peng-zhihui/HelloWord-Keyboard/2.Firmware/HelloWord-Dynamic-fw/Core/Src/tim.c

/**
  ******************************************************************************
  * @file    tim.c
  * @brief   This file provides code for the configuration
  *          of the TIM instances.
  ******************************************************************************
  * @attention
  *
  * <h2><center>&copy; Copyright (c) 2022 STMicroelectronics.
  * All rights reserved.</center></h2>
  *
  * This software component is licensed by ST under Ultimate Liberty license
  * SLA0044, the "License"; You may not use this file except in compliance with
  * the License. You may obtain a copy of the License at:
  *                             www.st.com/SLA0044
  *
  ******************************************************************************
  */

/* Includes ------------------------------------------------------------------*/
#include "tim.h"

/* USER CODE BEGIN 0 */
volatile int64_t encCntLoop[2];

/* USER CODE END 0 */

TIM_HandleTypeDef htim1;
TIM_HandleTypeDef htim7;
TIM_HandleTypeDef htim9;
TIM_HandleTypeDef htim10;
TIM_HandleTypeDef htim11;
TIM_HandleTypeDef htim13;
TIM_HandleTypeDef htim14;

/* TIM1 init function */
void MX_TIM1_Init(void)
{

  TIM_MasterConfigTypeDef sMasterConfig = {0};
  TIM_OC_InitTypeDef sConfigOC = {0};
  TIM_BreakDeadTimeConfigTypeDef sBreakDeadTimeConfig = {0};

  htim1.Instance = TIM1;
  htim1.Init.Prescaler = 0;
  htim1.Init.CounterMode = TIM_COUNTERMODE_CENTERALIGNED1;
  htim1.Init.Period = 4199;
  htim1.Init.ClockDivision = TIM_CLOCKDIVISION_DIV1;
  htim1.Init.RepetitionCounter = 0;
  htim1.Init.AutoReloadPreload = TIM_AUTORELOAD_PRELOAD_DISABLE;
  if (HAL_TIM_PWM_Init(&htim1) != HAL_OK)
  {
    Error_Handler();
  }
  sMasterConfig.MasterOutputTrigger = TIM_TRGO_OC4REF;
  sMasterConfig.MasterSlaveMode = TIM_MASTERSLAVEMODE_DISABLE;
  if (HAL_TIMEx_MasterConfigSynchronization(&htim1, &sMasterConfig) != HAL_OK)
  {
    Error_Handler();
  }
  sConfigOC.OCMode = TIM_OCMODE_PWM1;
  sConfigOC.Pulse = 0;
  sConfigOC.OCPolarity = TIM_OCPOLARITY_HIGH;
  sConfigOC.OCNPolarity = TIM_OCNPOLARITY_HIGH;
  sConfigOC.OCFastMode = TIM_OCFAST_DISABLE;
  sConfigOC.OCIdleState = TIM_OCIDLESTATE_RESET;
  sConfigOC.OCNIdleState = TIM_OCNIDLESTATE_RESET;
  if (HAL_TIM_PWM_ConfigChannel(&htim1, &sConfigOC, TIM_CHANNEL_1) != HAL_OK)
  {
    Error_Handler();
  }
  if (HAL_TIM_PWM_ConfigChannel(&htim1, &sConfigOC, TIM_CHANNEL_2) != HAL_OK)
  {
    Error_Handler();
  }
  if (HAL_TIM_PWM_ConfigChannel(&htim1, &sConfigOC, TIM_CHANNEL_3) != HAL_OK)
  {
    Error_Handler();
  }
  sBreakDeadTimeConfig.OffStateRunMode = TIM_OSSR_DISABLE;
  sBreakDeadTimeConfig.OffStateIDLEMode = TIM_OSSI_DISABLE;
  sBreakDeadTimeConfig.LockLevel = TIM_LOCKLEVEL_OFF;
  sBreakDeadTimeConfig.DeadTime = 0;
  sBreakDeadTimeConfig.BreakState = TIM_BREAK_DISABLE;
  sBreakDeadTimeConfig.BreakPolarity = TIM_BREAKPOLARITY_HIGH;
  sBreakDeadTimeConfig.AutomaticOutput = TIM_AUTOMATICOUTPUT_DISABLE;
  if (HAL_TIMEx_ConfigBreakDeadTime(&htim1, &sBreakDeadTimeConfig) != HAL_OK)
  {
    Error_Handler();
  }
  HAL_TIM_MspPostInit(&htim1);

}
/* TIM7 init function */
void MX_TIM7_Init(void)
{

  TIM_MasterConfigTypeDef sMasterConfig = {0};

  htim7.Instance = TIM7;
  htim7.Init.Prescaler = 83;
  htim7.Init.CounterMode = TIM_COUNTERMODE_UP;
  htim7.Init.Period = 9999;
  htim7.Init.AutoReloadPreload = TIM_AUTORELOAD_PRELOAD_ENABLE;
  if (HAL_TIM_Base_Init(&htim7) != HAL_OK)
  {
    Error_Handler();
  }
  sMasterConfig.MasterOutputTrigger = TIM_TRGO_RESET;
  sMasterConfig.MasterSlaveMode = TIM_MASTERSLAVEMODE_DISABLE;
  if (HAL_TIMEx_MasterConfigSynchronization(&htim7, &sMasterConfig) != HAL_OK)
  {
    Error_Handler();
  }
}
/* TIM9 init function */
void MX_TIM9_Init(void)
{

  TIM_ClockConfigTypeDef sClockSourceConfig = {0};

  htim9.Instance = TIM9;
  htim9.Init.Prescaler = 0;
  htim9.Init.CounterMode = TIM_COUNTERMODE_UP;
  htim9.Init.Period = 65535;
  htim9.Init.ClockDivision = TIM_CLOCKDIVISION_DIV1;
  htim9.Init.AutoReloadPreload = TIM_AUTORELOAD_PRELOAD_DISABLE;
  if (HAL_TIM_Base_Init(&htim9) != HAL_OK)
  {
    Error_Handler();
  }
  sClockSourceConfig.ClockSource = TIM_CLOCKSOURCE_INTERNAL;
  if (HAL_TIM_ConfigClockSource(&htim9, &sClockSourceConfig) != HAL_OK)
  {
    Error_Handler();
  }
}
/* TIM10 init function */
void MX_TIM10_Init(void)
{

  htim10.Instance = TIM10;
  htim10.Init.Prescaler = 167;
  htim10.Init.CounterMode = TIM_COUNTERMODE_UP;
  htim10.Init.Period = 9999;
  htim10.Init.ClockDivision = TIM_CLOCKDIVISION_DIV1;
  htim10.Init.AutoReloadPreload = TIM_AUTORELOAD_PRELOAD_ENABLE;
  if (HAL_TIM_Base_Init(&htim10) != HAL_OK)
  {
    Error_Handler();
  }
}
/* TIM11 init function */
void MX_TIM11_Init(void)
{

  htim11.Instance = TIM11;
  htim11.Init.Prescaler = 167;
  htim11.Init.CounterMode = TIM_COUNTERMODE_UP;
  htim11.Init.Period = 9999;
  htim11.Init.ClockDivision = TIM_CLOCKDIVISION_DIV1;
  htim11.Init.AutoReloadPreload = TIM_AUTORELOAD_PRELOAD_DISABLE;
  if (HAL_TIM_Base_Init(&htim11) != HAL_OK)
  {
    Error_Handler();
  }
}
/* TIM13 init function */
void MX_TIM13_Init(void)
{

  htim13.Instance = TIM13;
  htim13.Init.Prescaler = 83;
  htim13.Init.CounterMode = TIM_COUNTERMODE_UP;
  htim13.Init.Period = 9999;
  htim13.Init.ClockDivision = TIM_CLOCKDIVISION_DIV1;
  htim13.Init.AutoReloadPreload = TIM_AUTORELOAD_PRELOAD_DISABLE;
  if (HAL_TIM_Base_Init(&htim13) != HAL_OK)
  {
    Error_Handler();
  }
}
/* TIM14 init function */
void MX_TIM14_Init(void)
{

  htim14.Instance = TIM14;
  htim14.Init.Prescaler = 83;
  htim14.Init.CounterMode = TIM_COUNTERMODE_UP;
  htim14.Init.Period = 9999;
  htim14.Init.ClockDivision = TIM_CLOCKDIVISION_DIV1;
  htim14.Init.AutoReloadPreload = TIM_AUTORELOAD_PRELOAD_DISABLE;
  if (HAL_TIM_Base_Init(&htim14) != HAL_OK)
  {
    Error_Handler();
  }
}

void HAL_TIM_PWM_MspInit(TIM_HandleTypeDef* tim_pwmHandle)
{

  if(tim_pwmHandle->Instance==TIM1)
  {
    /* TIM1 clock enable */
    __HAL_RCC_TIM1_CLK_ENABLE();

    /* TIM1 interrupt Init */
    HAL_NVIC_SetPriority(TIM1_UP_TIM10_IRQn, 5, 0);
    HAL_NVIC_EnableIRQ(TIM1_UP_TIM10_IRQn);
    HAL_NVIC_SetPriority(TIM1_TRG_COM_TIM11_IRQn, 5, 0);
    HAL_NVIC_EnableIRQ(TIM1_TRG_COM_TIM11_IRQn);
  }
}

void HAL_TIM_Base_MspInit(TIM_HandleTypeDef* tim_baseHandle)
{

  if(tim_baseHandle->Instance==TIM7)
  {
    /* TIM7 clock enable */
    __HAL_RCC_TIM7_CLK_ENABLE();

    /* TIM7 interrupt Init */
    HAL_NVIC_SetPriority(TIM7_IRQn, 5, 0);
    HAL_NVIC_EnableIRQ(TIM7_IRQn);
  }
  else if(tim_baseHandle->Instance==TIM9)
  {
    /* TIM9 clock enable */
    __HAL_RCC_TIM9_CLK_ENABLE();
  }
  else if(tim_baseHandle->Instance==TIM10)
  {
    /* TIM10 clock enable */
    __HAL_RCC_TIM10_CLK_ENABLE();

    /* TIM10 interrupt Init */
    HAL_NVIC_SetPriority(TIM1_UP_TIM10_IRQn, 5, 0);
    HAL_NVIC_EnableIRQ(TIM1_UP_TIM10_IRQn);
  }
  else if(tim_baseHandle->Instance==TIM11)
  {
    /* TIM11 clock enable */
    __HAL_RCC_TIM11_CLK_ENABLE();

    /* TIM11 interrupt Init */
    HAL_NVIC_SetPriority(TIM1_TRG_COM_TIM11_IRQn, 5, 0);
    HAL_NVIC_EnableIRQ(TIM1_TRG_COM_TIM11_IRQn);
  }
  else if(tim_baseHandle->Instance==TIM13)
  {
    /* TIM13 clock enable */
    __HAL_RCC_TIM13_CLK_ENABLE();

    /* TIM13 interrupt Init */
    HAL_NVIC_SetPriority(TIM8_UP_TIM13_IRQn, 5, 0);
    HAL_NVIC_EnableIRQ(TIM8_UP_TIM13_IRQn);
  }
  else if(tim_baseHandle->Instance==TIM14)
  {
    /* TIM14 clock enable */
    __HAL_RCC_TIM14_CLK_ENABLE();

    /* TIM14 interrupt Init */
    HAL_NVIC_SetPriority(TIM8_TRG_COM_TIM14_IRQn, 5, 0);
    HAL_NVIC_EnableIRQ(TIM8_TRG_COM_TIM14_IRQn);
  }
}
void HAL_TIM_MspPostInit(TIM_HandleTypeDef* timHandle)
{

  GPIO_InitTypeDef GPIO_InitStruct = {0};
  if(timHandle->Instance==TIM1)
  {
    __HAL_RCC_GPIOB_CLK_ENABLE();
    __HAL_RCC_GPIOA_CLK_ENABLE();
    /**TIM1 GPIO Configuration
    PB0     ------> TIM1_CH2N
    PB1     ------> TIM1_CH3N
    PB13     ------> TIM1_CH1N
    PA8     ------> TIM1_CH1
    PA9     ------> TIM1_CH2
    PA10     ------> TIM1_CH3
    */
    GPIO_InitStruct.Pin = M0_PWM_BL_Pin|M0_PWM_CL_Pin|M0_PWM_AL_Pin;
    GPIO_InitStruct.Mode = GPIO_MODE_AF_PP;
    GPIO_InitStruct.Pull = GPIO_NOPULL;
    GPIO_InitStruct.Speed = GPIO_SPEED_FREQ_VERY_HIGH;
    GPIO_InitStruct.Alternate = GPIO_AF1_TIM1;
    HAL_GPIO_Init(GPIOB, &GPIO_InitStruct);

    GPIO_InitStruct.Pin = M0_PWM_AH_Pin|M0_PWM_BH_Pin|M0_PWM_CH_Pin;
    GPIO_InitStruct.Mode = GPIO_MODE_AF_PP;
    GPIO_InitStruct.Pull = GPIO_NOPULL;
    GPIO_InitStruct.Speed = GPIO_SPEED_FREQ_VERY_HIGH;
    GPIO_InitStruct.Alternate = GPIO_AF1_TIM1;
    HAL_GPIO_Init(GPIOA, &GPIO_InitStruct);

  }

}

void HAL_TIM_PWM_MspDeInit(TIM_HandleTypeDef* tim_pwmHandle)
{

  if(tim_pwmHandle->Instance==TIM1)
  {
    /* Peripheral clock disable */
    __HAL_RCC_TIM1_CLK_DISABLE();

    /* TIM1 interrupt Deinit */
  /* USER CODE BEGIN TIM1:TIM1_UP_TIM10_IRQn disable */
    /**
    * Uncomment the line below to disable the "TIM1_UP_TIM10_IRQn" interrupt
    * Be aware, disabling shared interrupt may affect other IPs
    */
    /* HAL_NVIC_DisableIRQ(TIM1_UP_TIM10_IRQn); */
  /* USER CODE END TIM1:TIM1_UP_TIM10_IRQn disable */

  /* USER CODE BEGIN TIM1:TIM1_TRG_COM_TIM11_IRQn disable */
    /**
    * Uncomment the line below to disable the "TIM1_TRG_COM_TIM11_IRQn" interrupt
    * Be aware, disabling shared interrupt may affect other IPs
    */
    /* HAL_NVIC_DisableIRQ(TIM1_TRG_COM_TIM11_IRQn); */
  /* USER CODE END TIM1:TIM1_TRG_COM_TIM11_IRQn disable */

  }
}

void HAL_TIM_Base_MspDeInit(TIM_HandleTypeDef* tim_baseHandle)
{

  if(tim_baseHandle->Instance==TIM7)
  {
    /* Peripheral clock disable */
    __HAL_RCC_TIM7_CLK_DISABLE();

    /* TIM7 interrupt Deinit */
    HAL_NVIC_DisableIRQ(TIM7_IRQn);
  }
  else if(tim_baseHandle->Instance==TIM9)
  {
    /* Peripheral clock disable */
    __HAL_RCC_TIM9_CLK_DISABLE();
  }
  else if(tim_baseHandle->Instance==TIM10)
  {
    /* Peripheral clock disable */
    __HAL_RCC_TIM10_CLK_DISABLE();

    /* TIM10 interrupt Deinit */
  /* USER CODE BEGIN TIM10:TIM1_UP_TIM10_IRQn disable */
    /**
    * Uncomment the line below to disable the "TIM1_UP_TIM10_IRQn" interrupt
    * Be aware, disabling shared interrupt may affect other IPs
    */
    /* HAL_NVIC_DisableIRQ(TIM1_UP_TIM10_IRQn); */
  /* USER CODE END TIM10:TIM1_UP_TIM10_IRQn disable */

  }
  else if(tim_baseHandle->Instance==TIM11)
  {
    /* Peripheral clock disable */
    __HAL_RCC_TIM11_CLK_DISABLE();

    /* TIM11 interrupt Deinit */
  /* USER CODE BEGIN TIM11:TIM1_TRG_COM_TIM11_IRQn disable */
    /**
    * Uncomment the line below to disable the "TIM1_TRG_COM_TIM11_IRQn" interrupt
    * Be aware, disabling shared interrupt may affect other IPs
    */
    /* HAL_NVIC_DisableIRQ(TIM1_TRG_COM_TIM11_IRQn); */
  /* USER CODE END TIM11:TIM1_TRG_COM_TIM11_IRQn disable */

  }
  else if(tim_baseHandle->Instance==TIM13)
  {
    /* Peripheral clock disable */
    __HAL_RCC_TIM13_CLK_DISABLE();

    /* TIM13 interrupt Deinit */
    HAL_NVIC_DisableIRQ(TIM8_UP_TIM13_IRQn);
  }
  else if(tim_baseHandle->Instance==TIM14)
  {
    /* Peripheral clock disable */
    __HAL_RCC_TIM14_CLK_DISABLE();

    /* TIM14 interrupt Deinit */
    HAL_NVIC_DisableIRQ(TIM8_TRG_COM_TIM14_IRQn);
  }
}

/* USER CODE BEGIN 1 */
void HAL_TIM_IC_CaptureCallback(TIM_HandleTypeDef *htim)
{
    if (htim->Instance->SR & 0x01) // count overflow
    {
        if (htim->Instance->CR1 & 0x10) // count up
        {
            if (htim->Instance == TIM2)
                encCntLoop[0]--;
            else if (htim->Instance == TIM3)
                encCntLoop[1]--;
        } else                          // count down
        {
            if (htim->Instance == TIM2)
                encCntLoop[0]++;
            else if (htim->Instance == TIM3)
                encCntLoop[1]++;
        }

        htim->Instance->SR = htim->Instance->SR & 0xFE; // clear flag
    }
}

int64_t GetCntLoop(TIM_TypeDef *tim)
{
    if (tim == TIM2)
    {
        return encCntLoop[0];
    } else if (tim == TIM3)
    {
        return encCntLoop[1];
    }
}

void ClearCntLoop(TIM_TypeDef *tim)
{
    if (tim == TIM2)
    {
        encCntLoop[0] = 0;
    } else if (tim == TIM3)
    {
        encCntLoop[1] = 0;
    }
}

int64_t GetEncoderCount(TIM_TypeDef *tim)
{
    if (tim == TIM2)
    {
        return encCntLoop[0] * 65536 + TIM2->CNT;
    } else if (tim == TIM3)
    {
        return encCntLoop[1] * 65536 + TIM3->CNT;
    }
}
/* USER CODE END 1 */

/************************ (C) COPYRIGHT STMicroelectronics *****END OF FILE****/
