peng-zhihui/HelloWord-Keyboard/2.Firmware/HelloWord-Dynamic-fw/Ctrl/Sensor/CurrentSense/current_sense_base.h

#ifndef CTRL_FOC_LITE_FW_CURRENT_SENSE_BASE_H
#define CTRL_FOC_LITE_FW_CURRENT_SENSE_BASE_H

#include "Ctrl/Driver/driver_base.h"
#include "Ctrl/Motor/math_utils.h"


class CurrentSenseBase
{
public:
    // Decided by hardware & configuration
    static constexpr uint16_t ADC_CONVERT_TIME_US = 8;
    static constexpr uint32_t ADC_RESOLUTION = 4096;
    static constexpr float ADC_VOLTAGE_RANGE = 3.3f;

    uint8_t sector;
    float pwmDutyA;
    float pwmDutyB;
    float pwmDutyC;

    /*
     * Need to adjust considering ADC sample time,
     * for example Threshold = AAR_ADC / PWM_Period = 1500/1799 ≈ 0.84,
     * so when one phase has output a pwm duty cycle more than 0.84 then
     * this phase's current sense may not be used.
     */
    float dropOnePhaseDutyThreshold = 0.75f;

    virtual void Init() = 0;
    virtual PhaseCurrent_t GetPhaseCurrents() = 0;
    virtual float GetDcCurrent(float _angleElectrical);
    DqCurrent_t GetFocCurrents(float _angleElectrical);


protected:
    float iAlpha, iBeta;
};


#endif //CTRL_FOC_LITE_FW_CURRENT_SENSE_BASE_H
