peng-zhihui/HelloWord-Keyboard/2.Firmware/HelloWord-Dynamic-fw/Platform/Communication/communication.hpp

#ifndef COMMANDS_H
#define COMMANDS_H

#ifdef __cplusplus
extern "C" {
#endif

#include <cmsis_os.h>

void InitCommunication(void);
void CommitProtocol();
void CommunicationTask(void *ctx);
void UsbDeferredInterruptTask(void *ctx);

#ifdef __cplusplus
}

#include <functional>
#include <limits>
#include "ascii_processor.hpp"
#include "interface_usb.hpp"
#include "interface_uart.hpp"

#define COMMIT_PROTOCOL \
using treeType = decltype(MakeObjTree());\
uint8_t treeBuffer[sizeof(treeType)];\
void CommitProtocol()\
{\
    auto treePtr = new(treeBuffer) treeType(MakeObjTree());\
    fibre_publish(*treePtr);\
}\


#endif
#endif /* COMMANDS_H */
