peng-zhihui/HelloWord-Keyboard/2.Firmware/HelloWord-Dynamic-fw/Platform/Communication/ascii_processor.cpp

/*
* The ASCII protocol is a simpler, human readable alternative to the main native
* protocol.
* In the future this protocol might be extended to support selected GCode commands.
* For a list of supported commands see doc/ascii-protocol.md
*/

/* Includes ------------------------------------------------------------------*/

#include "common_inc.h"
#include "ascii_processor.hpp"

/* Private macros ------------------------------------------------------------*/
/* Private typedef -----------------------------------------------------------*/
/* Global constant data ------------------------------------------------------*/
/* Global variables ----------------------------------------------------------*/
/* Private constant data -----------------------------------------------------*/
#define MAX_LINE_LENGTH 256
#define TO_STR_INNER(s) #s
#define TO_STR(s) TO_STR_INNER(s)
/* Private variables ---------------------------------------------------------*/
/* Private function prototypes -----------------------------------------------*/
/* Function implementations --------------------------------------------------*/


// @brief Executes an ASCII protocol command
// @param buffer buffer of ASCII encoded characters
// @param len size of the buffer
void ASCII_protocol_process_line(const uint8_t *buffer, size_t len, StreamSink &response_channel)
{
    static_assert(sizeof(char) == sizeof(uint8_t));

    // scan line to find beginning of checksum and prune comment
    uint8_t checksum = 0;
    size_t checksum_start = SIZE_MAX;
    for (size_t i = 0; i < len; ++i)
    {
        if (buffer[i] == ';')
        { // ';' is the comment start char
            len = i;
            break;
        }
        if (checksum_start > i)
        {
            if (buffer[i] == '*')
            {
                checksum_start = i + 1;
            } else
            {
                checksum ^= buffer[i];
            }
        }
    }

    // copy everything into a local buffer so we can insert null-termination
    char cmd[MAX_LINE_LENGTH + 1];
    if (len > MAX_LINE_LENGTH) len = MAX_LINE_LENGTH;
    memcpy(cmd, buffer, len);

    // optional checksum validation
    bool use_checksum = (checksum_start < len);
    if (use_checksum)
    {
        unsigned int received_checksum;
        sscanf((const char *) cmd + checksum_start, "%u", &received_checksum);
        if (received_checksum != checksum)
            return;
        len = checksum_start - 1; // prune checksum and asterisk
    }

    cmd[len] = 0; // null-terminate

    OnAsciiCmd(cmd, len, response_channel);
}

void ASCII_protocol_parse_stream(const uint8_t *buffer, size_t len, StreamSink &response_channel)
{
    static uint8_t parse_buffer[MAX_LINE_LENGTH];
    static bool read_active = true;
    static uint32_t parse_buffer_idx = 0;

    while (len--)
    {
        // if the line becomes too long, reset buffer and wait for the next line
        if (parse_buffer_idx >= MAX_LINE_LENGTH)
        {
            read_active = false;
            parse_buffer_idx = 0;
        }

        // Fetch the next char
        uint8_t c = *(buffer++);
        bool is_end_of_line = (c == '\r' || c == '\n' || c == '!');
        if (is_end_of_line)
        {
            if (read_active)
                ASCII_protocol_process_line(parse_buffer, parse_buffer_idx, response_channel);
            parse_buffer_idx = 0;
            read_active = true;
        } else
        {
            if (read_active)
            {
                parse_buffer[parse_buffer_idx++] = c;
            }
        }
    }
}
