peng-zhihui/HelloWord-Keyboard/2.Firmware/HelloWord-Dynamic-fw/Core/Inc/adc.h

/**
  ******************************************************************************
  * @file    adc.h
  * @brief   This file contains all the function prototypes for
  *          the adc.c file
  ******************************************************************************
  * @attention
  *
  * <h2><center>&copy; Copyright (c) 2022 STMicroelectronics.
  * All rights reserved.</center></h2>
  *
  * This software component is licensed by ST under Ultimate Liberty license
  * SLA0044, the "License"; You may not use this file except in compliance with
  * the License. You may obtain a copy of the License at:
  *                             www.st.com/SLA0044
  *
  ******************************************************************************
  */
/* Define to prevent recursive inclusion -------------------------------------*/
#ifndef __ADC_H__
#define __ADC_H__

#ifdef __cplusplus
extern "C" {
#endif

/* Includes ------------------------------------------------------------------*/
#include "main.h"

extern ADC_HandleTypeDef hadc1;

/* USER CODE BEGIN Private defines */
#define ADC_CH1 ADC_CHANNEL_12
#define ADC_CH2 ADC_CHANNEL_13
#define ADC_CH3 ADC_CHANNEL_14
#define ADC_CH4 ADC_CHANNEL_15


#define ADC_CHANNEL_REF 16
#define ADC_CHANNEL_TEMP 4
extern uint16_t adc1ValBuf[ADC_CHANNEL_REF + 1];


/* USER CODE END Private defines */

void MX_ADC1_Init(void);

/* USER CODE BEGIN Prototypes */
float AdcGetChipTemperature();

float AdcGetVoltage(uint32_t _channel);

uint16_t AdcGetRaw(uint32_t _channel);

/* USER CODE END Prototypes */

#ifdef __cplusplus
}
#endif

#endif /* __ADC_H__ */

/************************ (C) COPYRIGHT STMicroelectronics *****END OF FILE****/
