peng-zhihui/HelloWord-Keyboard/2.Firmware/HelloWord-Dynamic-fw/Platform/Communication/interface_usb.hpp

#ifndef __INTERFACE_USB_HPP
#define __INTERFACE_USB_HPP

#ifdef __cplusplus

#include "BSP//fibre/inc/protocol.hpp"

extern StreamSink *usb_stream_output_ptr;

extern "C" {
#endif

#include <cmsis_os.h>
#include <stdint.h>

typedef struct
{
    uint32_t rx_cnt;
    uint32_t tx_cnt;
    uint32_t tx_overrun_cnt;
} USBStats_t;

extern USBStats_t usb_stats_;

void usb_rx_process_packet(uint8_t *buf, uint32_t len, uint8_t endpoint_pair);
void StartUsbServer(void);

#ifdef __cplusplus
}
#endif

#endif // __INTERFACE_USB_HPP
