peng-zhihui/HelloWord-Keyboard/2.Firmware/HelloWord-Keyboard-fw/UserApp/common_inc.h

#ifndef LOOP_H
#define LOOP_H

#ifdef __cplusplus
extern "C" {
#endif
/*---------------------------- C Scope ---------------------------*/
#include "stdint-gcc.h"
#include "stm32f1xx_hal.h"
#include "main.h"
#include "tim.h"
#include "usbd_customhid.h"
#include "usb_device.h"


void Main();
void OnUartCmd(uint8_t* _data, uint16_t _len);
void OnTimerCallback();

#ifdef __cplusplus
}


/*---------------------------- C++ Scope ---------------------------*/
#include "HelloWord/Utils/Memory/random_flash_interface.h"


#endif
#endif
