peng-zhihui/HelloWord-Keyboard/2.Firmware/HelloWord-Dynamic-fw/Platform/Utils/time_utils.cpp

#include "time_utils.h"
#include "stm32f4xx_hal.h"


__IO uint32_t m, tms, u, t0;

void delay(uint32_t _ms)
{
    t0 = micros();
    while (micros() - t0 < _ms * 1000)
        __NOP();
}


void delayMicroSeconds(uint32_t _us)
{
    _us *= 28; // Need to be tuned for different CPU
    while (_us--) __NOP();
}


__STATIC_INLINE uint32_t LL_SYSTICK_IsActiveCounterFlag()
{
    return ((SysTick->CTRL & SysTick_CTRL_COUNTFLAG_Msk) == (SysTick_CTRL_COUNTFLAG_Msk));
}


uint64_t micros()
{
    /* Ensure COUNTFLAG is reset by reading SysTick control and status register */
    LL_SYSTICK_IsActiveCounterFlag();
    m = HAL_GetTick();
    tms = SysTick->LOAD + 1;
    u = tms - SysTick->VAL;
    if (LL_SYSTICK_IsActiveCounterFlag())
    {
        m = HAL_GetTick();
        u = tms - SysTick->VAL;
    }
    return (m * 1000 + (u * 1000) / tms);
}


uint32_t millis()
{
    return HAL_GetTick();
}
